fkorhone/HY-Controlboard/documents/pages/heading.pdf

# HY controlboard

Version 2.3 Schematics

https://github.com/fkorhone/HY-Controlboard

## Known issues and changes:

## Date
